joanperelopez/HF-Noise-Canceller/IMAGES/Noise Canceller 2.0_t.png

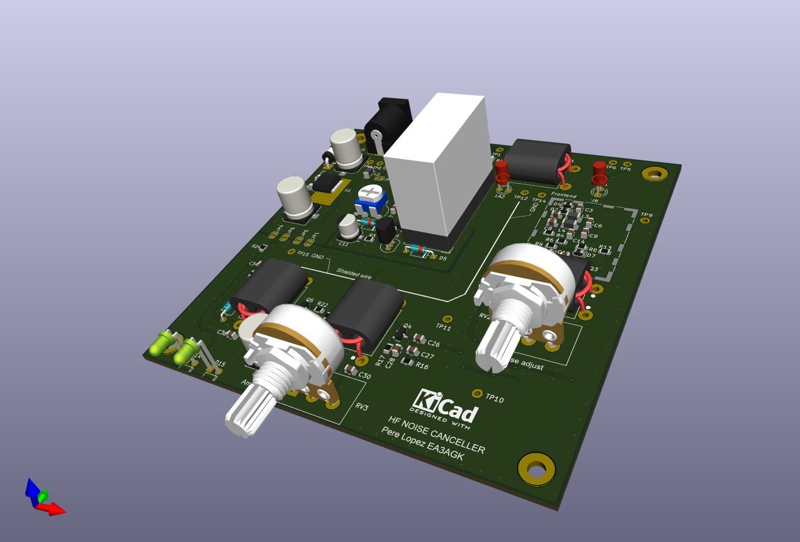
IMAGES/Noise Canceller 2.0_t.png
