joanperelopez/HF-Noise-Canceller/IMAGES/Top view.png

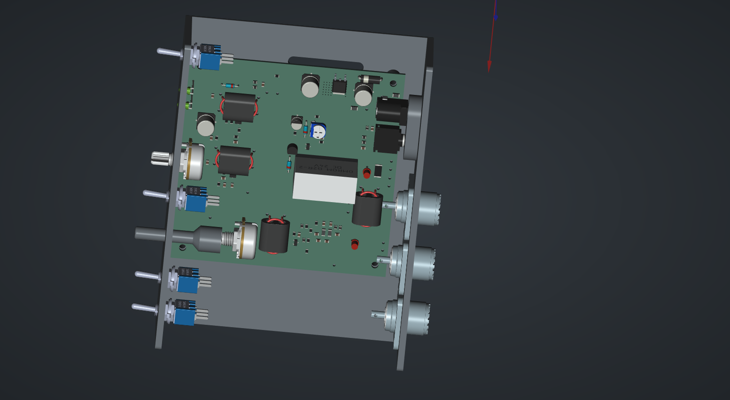
IMAGES/Top view.png
