joanperelopez/HF-Noise-Canceller/IMAGES/WhatsApp Image 2025-04-19 at 12.38.03.jpeg

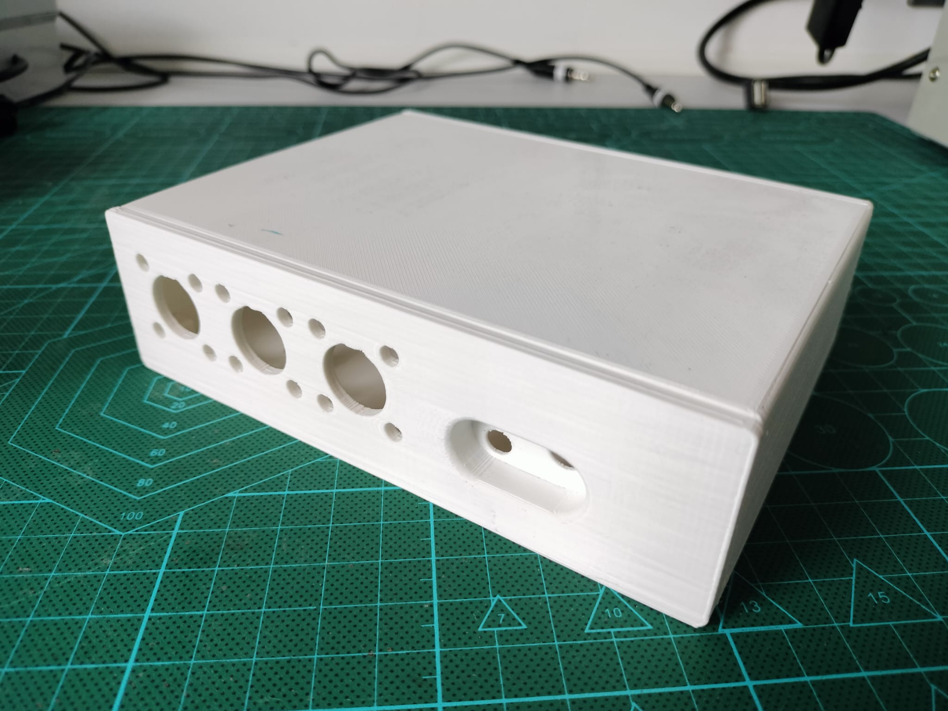
IMAGES/WhatsApp Image 2025-04-19 at 12.38.03.jpeg
