joanperelopez/HF-Noise-Canceller/IMAGES/WhatsApp Image 2025-04-19 at 12.46.19.jpeg

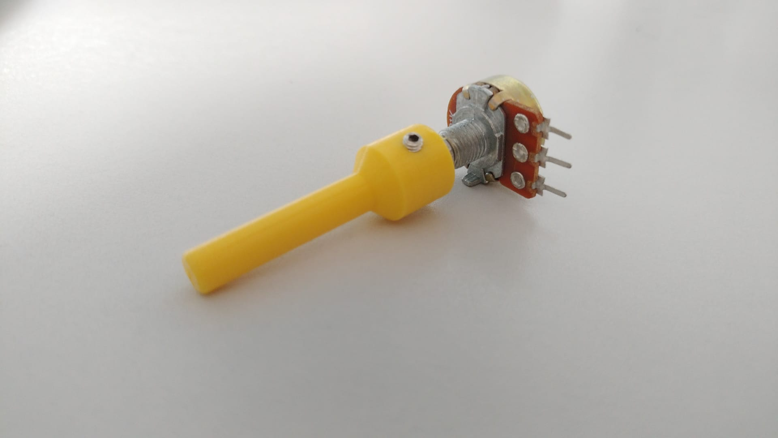
IMAGES/WhatsApp Image 2025-04-19 at 12.46.19.jpeg
